Professor-plum/stm8_minibadges/Doom/doom.h

const uint16_t pallet[] = { 0x0000, 0x2901, 0x5A04, 0x7A85, 0x4184, 0x9B07, 0xB388, 0x6286, 0xCC0A, 0xFD0B, 0xDC8C, 0x9C0C, 0xED0E, 0xFD8F, 0xFD90, 0x0010, 0x630C, 0xB596, 0xFE97, 0x5820, 0x49A3, 0x6A24, 0x2124, 0x82A6, 0x4228, 0x52AA, 0xBAAA, 0x73AE, 0xECB2, 0x94B2, 0xFE34, 0xA534, 0xFEB7, 0x4208, 0x3142, 0x9AC2, 0x78C3, 0x8945, 0xA347, 0x39C7, 0xBBC9, 0xD44B, 0x5ACB, 0xE4CD, 0x6B4D, 0xF54F, 0xDBCF, 0xFDD2, 0xAD55, 0xCE59, 0xDEDB, 0x3962, 0x51E3, 0x7265, 0x8AE6, 0x2965, 0xAB68, 0xCBE9, 0x4A69, 0x7BEF, 0x9CF3, 0xFDF3, 0xFE76, 0xDEFB, 0xEF7D, };

const uint8_t doom1_raw[] = {
	0x00, 0x00, 0x00, 0x00, 0x00, 0x00, 0x14, 0x02, 0x02, 0x02, 0x15, 0x35, 0x35, 0x35, 0x35, 0x35, 
	0x15, 0x02, 0x02, 0x14, 0x00, 0x00, 0x00, 0x00, 0x00, 0x00, 0x00, 0x00, 0x00, 0x00, 0x22, 0x02, 
	0x34, 0x03, 0x36, 0x38, 0x28, 0x08, 0x08, 0x08, 0x28, 0x38, 0x05, 0x35, 0x02, 0x34, 0x02, 0x22, 
	0x00, 0x00, 0x00, 0x00, 0x00, 0x00, 0x00, 0x22, 0x02, 0x35, 0x36, 0x38, 0x28, 0x39, 0x08, 0x28, 
	0x06, 0x05, 0x05, 0x05, 0x36, 0x36, 0x35, 0x35, 0x34, 0x14, 0x22, 0x00, 0x00, 0x00, 0x00, 0x00, 
	0x00, 0x22, 0x35, 0x17, 0x35, 0x36, 0x05, 0x06, 0x17, 0x38, 0x36, 0x26, 0x35, 0x35, 0x35, 0x35, 
	0x02, 0x34, 0x22, 0x22, 0x01, 0x00, 0x00, 0x00, 0x00, 0x00, 0x01, 0x33, 0x02, 0x35, 0x02, 0x36, 
	0x05, 0x36, 0x36, 0x36, 0x36, 0x14, 0x36, 0x02, 0x14, 0x02, 0x14, 0x22, 0x01, 0x01, 0x01, 0x01, 
	0x00, 0x00, 0x00, 0x00, 0x01, 0x33, 0x14, 0x34, 0x02, 0x36, 0x34, 0x05, 0x15, 0x15, 0x36, 0x15, 
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
	0x33, 0x15, 0x26, 0x2D, 0x36, 0x35, 0x08, 0x2D, 0x0A, 0x03, 0x00, 0x22, 0x22, 0x05, 0x34, 0x15, 
	0x36, 0x05, 0x36, 0x08, 0x0A, 0x2D, 0x0A, 0x0A, 0x39, 0x38, 0x08, 0x26, 0x05, 0x1E, 0x29, 0x35, 
	0x08, 0x3D, 0x0E, 0x03, 0x00, 0x22, 0x22, 0x15, 0x36, 0x34, 0x17, 0x17, 0x17, 0x05, 0x28, 0x39, 
	0x39, 0x08, 0x2B, 0x2D, 0x28, 0x36, 0x05, 0x0A, 0x2F, 0x35, 0x28, 0x0E, 0x3E, 0x36, 0x00, 0x00, 
	0x22, 0x22, 0x06, 0x36, 0x17, 0x17, 0x17, 0x17, 0x17, 0x17, 0x26, 0x0A, 0x1E, 0x0A, 0x38, 0x2B, 
	0x38, 0x29, 0x2B, 0x26, 0x38, 0x2B, 0x0C, 0x36, 0x00, 0x00, 0x22, 0x22, 0x36, 0x36, 0x17, 0x17, 
	0x05, 0x36, 0x36, 0x05, 0x28, 0x2F, 0x0C, 0x35, 0x15, 0x33, 0x34, 0x34, 0x35, 0x35, 0x35, 0x08, 
	0x29, 0x36, 0x00, 0x00, 0x00, 0x22, 0x34, 0x36, 0x17, 0x17, 0x38, 0x28, 0x38, 0x05, 0x29, 0x2D, 
	0x28, 0x35, 0x26, 0x26, 0x06, 0x05, 0x05, 0x26, 0x35, 0x38, 0x06, 0x02, 0x00, 0x00, 0x00, 0x00, 
	0x00, 0x36, 0x17, 0x17, 0x26, 0x39, 0x28, 0x05, 0x08, 0x0A, 0x05, 0x36, 0x08, 0x0C, 0x08, 0x0A, 
	0x2D, 0x26, 0x02, 0x26, 0x06, 0x02, 0x00, 0x00, 0x00, 0x00, 0x00, 0x00, 0x00, 0x17, 0x36, 0x38, 
	0x28, 0x05, 0x28, 0x2B, 0x17, 0x05, 0x18, 0x2A, 0x2C, 0x3B, 0x18, 0x18, 0x02, 0x26, 0x08, 0x14, 
	0x00, 0x00, 0x00, 0x00, 0x00, 0x00, 0x00, 0x00, 0x17, 0x36, 0x38, 0x05, 0x38, 0x2B, 0x26, 0x18, 
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
	};
