Professor-plum/stm8_minibadges/Metroid/metroid.h

const uint16_t pallet[] = { 0x0000, 0xD940, 0xFCC7, 0x04A0, 0x0411, 0xFE3B, 0x21DD, 0x5CBF, };

const uint8_t brick1_raw[] = {
	0x07, 0x77, 0x77, 0x70, 0x07, 0x77, 0x77, 0x70, 0x77, 0x77, 0x77, 0x77, 0x77, 0x77, 0x77, 0x74, 
	0x77, 0x66, 0x66, 0x66, 0x66, 0x66, 0x66, 0x44, 0x77, 0x60, 0x66, 0x66, 0x66, 0x66, 0x06, 0x44, 
	0x77, 0x66, 0x66, 0x66, 0x66, 0x66, 0x66, 0x44, 0x77, 0x66, 0x77, 0x77, 0x44, 0x44, 0x66, 0x44, 
	0x77, 0x66, 0x60, 0x00, 0x00, 0x00, 0x66, 0x44, 0x07, 0x66, 0x77, 0x77, 0x44, 0x44, 0x66, 0x40, 
	0x07, 0x66, 0x60, 0x00, 0x00, 0x00, 0x66, 0x40, 0x77, 0x66, 0x77, 0x77, 0x44, 0x44, 0x66, 0x44, 
	0x77, 0x66, 0x60, 0x00, 0x00, 0x00, 0x66, 0x44, 0x77, 0x66, 0x66, 0x66, 0x66, 0x66, 0x66, 0x44, 
	0x77, 0x60, 0x66, 0x66, 0x66, 0x66, 0x06, 0x44, 0x77, 0x66, 0x66, 0x66, 0x66, 0x66, 0x66, 0x44, 
	0x74, 0x44, 0x44, 0x44, 0x44, 0x44, 0x44, 0x44, 0x04, 0x44, 0x44, 0x40, 0x04, 0x44, 0x44, 0x40, 
	};

const uint8_t brick2_raw[] = {
	0x00, 0x77, 0x77, 0x70, 0x00, 0x07, 0x70, 0x00, 0x07, 0x77, 0x74, 0x47, 0x77, 0x74, 0x44, 0x40, 
	0x77, 0x74, 0x44, 0x44, 0x44, 0x00, 0x00, 0x04, 0x07, 0x77, 0x00, 0x00, 0x00, 0x00, 0x44, 0x44, 
	0x00, 0x00, 0x07, 0x77, 0x44, 0x40, 0x00, 0x00, 0x77, 0x77, 0x74, 0x44, 0x40, 0x00, 0x00, 0x40, 
	0x44, 0x74, 0x77, 0x00, 0x00, 0x04, 0x44, 0x44, 0x00, 0x04, 0x44, 0x40, 0x40, 0x00, 0x00, 0x00, 
	0x77, 0x00, 0x00, 0x07, 0x74, 0x40, 0x00, 0x44, 0x44, 0x77, 0x77, 0x74, 0x44, 0x44, 0x44, 0x44, 
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
	0x00, 0x01, 0x11, 0x11, 0x00, 0x00, 0x00, 0x00, 0x00, 0x00, 0x00, 0x00, 0x00, 0x00, 0x01, 0x11, 
	0x33, 0x10, 0x00, 0x00, 0x00, 0x00, 0x00, 0x00, 0x00, 0x00, 0x00, 0x00, 0x13, 0x11, 0x11, 0x00, 
	0x00, 0x00, 0x00, 0x00, 0x00, 0x00, 0x00, 0x00, 0x00, 0x00, 0x11, 0x11, 0x10, 0x00, 0x00, 0x00, 
	};
