Professor-plum/stm8_minibadges/Pitfall/pitfall.h

const uint16_t pallet[] = { 0x3200, 0x1240, 0x5C85, 0x75AD, 0x1B11, 0x0980, 0xFCD6, };

const uint8_t harry_raw[] = {
	0x00, 0x00, 0x22, 0x22, 0x22, 0x22, 0x22, 0x22, 0x66, 0x66, 0x22, 0x66, 0x22, 0x22, 0x22, 0x22, 
	0x66, 0x66, 0x22, 0x66, 0x22, 0x22, 0x22, 0x22, 0x66, 0x22, 0x22, 0x66, 0x22, 0x22, 0x22, 0x22, 
	0x33, 0x33, 0x22, 0x33, 0x22, 0x22, 0x22, 0x22, 0x33, 0x33, 0x33, 0x33, 0x22, 0x22, 0x22, 0x22, 
	0x33, 0x33, 0x22, 0x22, 0x22, 0x22, 0x22, 0x22, 0x33, 0x33, 0x22, 0x22, 0x22, 0x22, 0x22, 0x22, 
	0x33, 0x33, 0x22, 0x22, 0x22, 0x22, 0x22, 0x22, 0x33, 0x33, 0x22, 0x22, 0x22, 0x22, 0x22, 0x22, 
	0x33, 0x33, 0x22, 0x22, 0x22, 0x22, 0x22, 0x22, 0x11, 0x11, 0x22, 0x11, 0x11, 0x11, 0x22, 0x22, 
	0x11, 0x11, 0x11, 0x11, 0x22, 0x11, 0x11, 0x22, 0x11, 0x11, 0x11, 0x11, 0x22, 0x22, 0x11, 0x22, 
	0x22, 0x11, 0x11, 0x22, 0x22, 0x22, 0x11, 0x11, 
	};

const uint8_t gator1_raw[] = {
	0x22, 0x22, 0x22, 0x22, 0x22, 0x22, 0x22, 0x22, 0x22, 0x22, 0x22, 0x22, 0x22, 0x22, 0x22, 0x22, 
	0x44, 0x44, 0x44, 0x44, 0x44, 0x55, 0x44, 0x44, 0x44, 0x44, 0x44, 0x44, 0x44, 0x55, 0x55, 0x44, 
	0x55, 0x55, 0x55, 0x55, 0x55, 0x55, 0x55, 0x55, 0x44, 0x55, 0x44, 0x55, 0x44, 0x55, 0x44, 0x55, 
	0x55, 0x44, 0x55, 0x44, 0x55, 0x44, 0x55, 0x55, 0x55, 0x55, 0x55, 0x55, 0x55, 0x55, 0x55, 0x55, 
	};

const uint8_t gator2_raw[] = {
	0x55, 0x22, 0x22, 0x22, 0x22, 0x22, 0x22, 0x22, 0x55, 0x55, 0x55, 0x22, 0x22, 0x22, 0x22, 0x22, 
	0x55, 0x44, 0x55, 0x55, 0x55, 0x22, 0x55, 0x22, 0x44, 0x44, 0x55, 0x44, 0x55, 0x55, 0x55, 0x44, 
	0x44, 0x44, 0x44, 0x44, 0x55, 0x44, 0x55, 0x55, 0x44, 0x44, 0x44, 0x44, 0x44, 0x44, 0x55, 0x55, 
	0x55, 0x44, 0x55, 0x44, 0x55, 0x44, 0x55, 0x55, 0x55, 0x55, 0x55, 0x55, 0x55, 0x55, 0x55, 0x55, 
	};
